geoffgun15/openmice/output/editor-preview.jpg

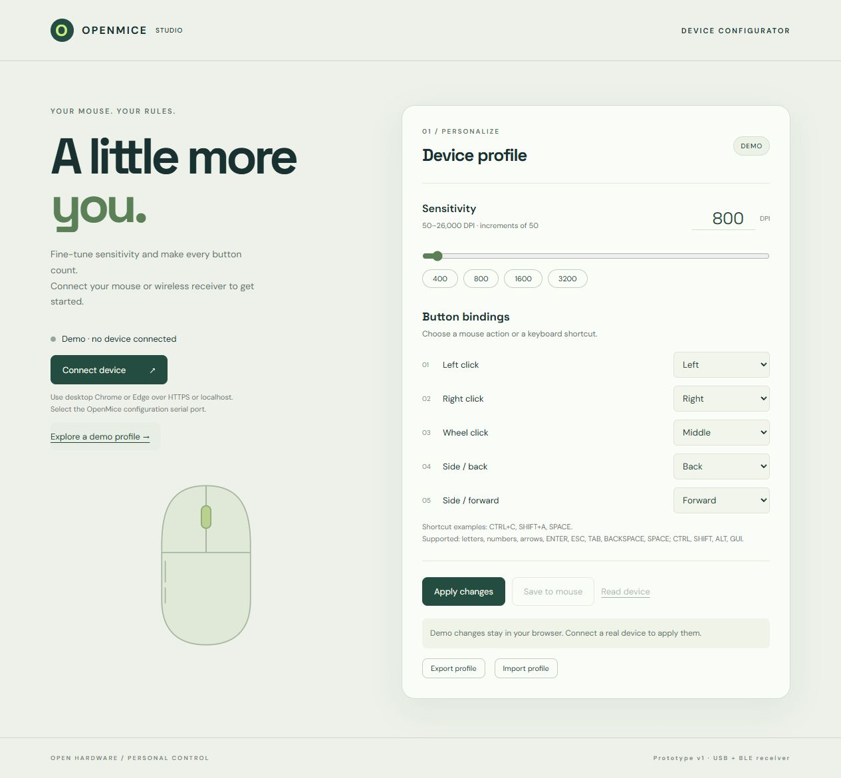
output/editor-preview.jpg
