geoffgun15/openmice/output/hardware/mouse/board-3d.png

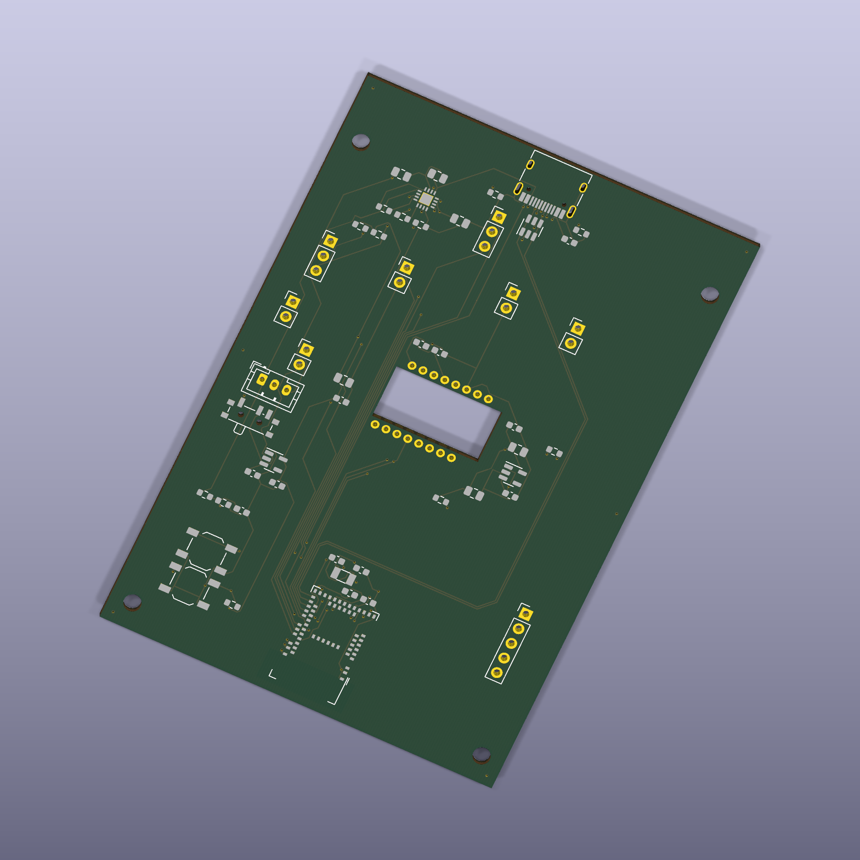
output/hardware/mouse/board-3d.png
