geoffgun15/openmice/output/hardware/mouse/assembly-top.png

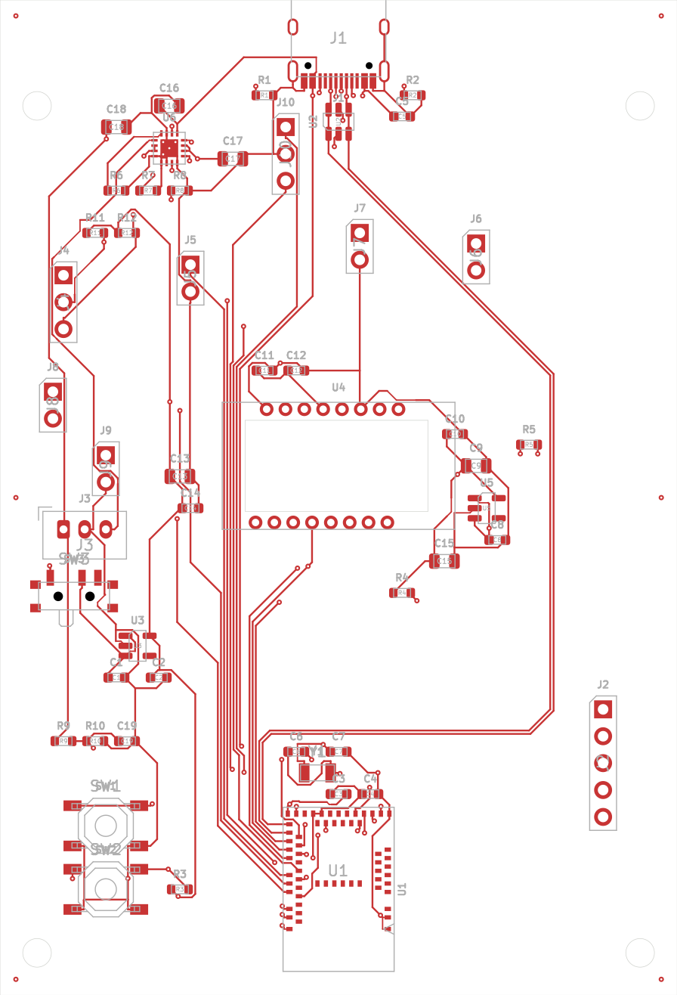
output/hardware/mouse/assembly-top.png
