geoffgun15/openmice/output/hardware/receiver/assembly-top.png

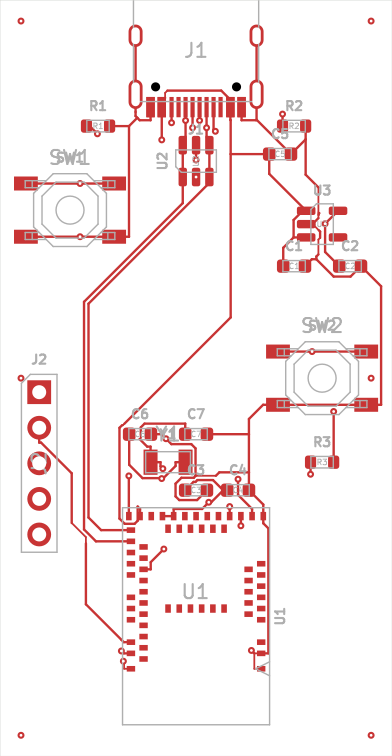
output/hardware/receiver/assembly-top.png
