geoffgun15/openmice/firmware/common/init_sequence.py

# Startup table checked against supplied PAW3395 v1.3 section 6.2.
INIT_SEQUENCE = ((127, 7), (64, 65), (127, 0), (64, 128), (127, 14), (85, 13), (86, 27), (87, 232), (88, 213), (127, 20), (66, 188), (67, 116), (75, 32), (77, 0), (83, 14), (127, 5), (67, 100), (68, 4), (77, 6), (81, 64), (83, 64), (85, 202), (90, 232), (91, 234), (97, 49), (98, 100), (109, 184), (110, 15), (112, 2), (74, 42), (96, 38), (127, 6), (109, 112), (110, 96), (111, 4), (83, 2), (85, 17), (122, 1), (125, 81), (127, 7), (65, 16), (66, 50), (67, 0), (127, 8), (113, 79), (127, 9), (98, 31), (99, 31), (101, 3), (102, 3), (103, 31), (104, 31), (105, 3), (106, 3), (108, 31), (109, 31), (81, 4), (83, 32), (84, 32), (113, 12), (114, 7), (115, 7), (127, 10), (74, 20), (76, 20), (85, 25), (127, 20), (75, 48), (76, 3), (97, 11), (98, 10), (99, 2), (127, 21), (76, 2), (86, 2), (65, 145), (77, 10), (127, 12), (74, 16), (75, 12), (76, 64), (65, 37), (85, 24), (86, 20), (73, 10), (66, 0), (67, 45), (68, 12), (84, 26), (90, 13), (95, 30), (91, 5), (94, 15), (97, 34), (98, 65), (127, 13), (72, 221), (79, 3), (82, 73), (81, 0), (84, 91), (83, 0), (86, 100), (85, 0), (88, 165), (87, 2), (90, 41), (91, 71), (92, 129), (93, 64), (113, 220), (112, 7), (115, 0), (114, 8), (117, 220), (116, 7), (119, 0), (118, 8), (127, 16), (76, 208), (127, 0), (79, 99), (78, 0), (82, 99), (81, 0), (84, 84), (90, 16), (119, 79), (71, 1), (91, 64), (100, 96), (101, 6), (102, 19), (103, 15), (120, 1), (121, 156), (64, 0), (85, 2), (35, 112), (34, 1))
